shapoco/sdr-jjy/apps/jjymon_pico/src/images.cpp

#include <stdint.h>
namespace shapoco::jjymon {

uint8_t bmp_bit_icons[] = {
    16, 0, 4, 0,
    0x60, 0xf6, 0x46, 0xf9, 0x46, 0xf9, 0x40, 0xf6, 
};

uint8_t bmp_meter_frame[] = {
    32, 0, 8, 0,
    0x00, 0xf0, 0x0f, 0x00, 0x80, 0x0f, 0xf0, 0x01, 0x70, 0x00, 0x00, 0x0e, 0x0c, 0x00, 0x00, 0x30, 
    0x03, 0x00, 0x00, 0xc0, 0x01, 0x00, 0x00, 0x80, 0x02, 0x00, 0x00, 0x40, 0x02, 0x00, 0x00, 0x40, 
};

uint8_t bmp_icon_beat[] = {
    8, 0, 5, 0,
    0x10, 0x54, 0xff, 0x2a, 0x08, 
};

}
